padeler/picbox/photos/20190130_210322.jpg

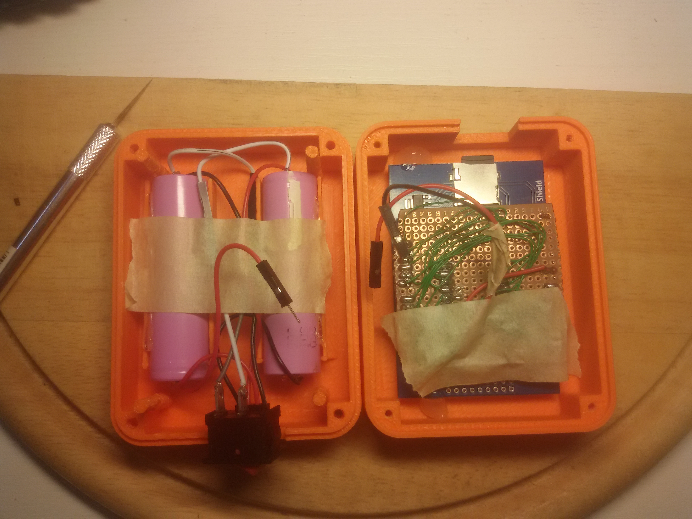
photos/20190130_210322.jpg
